rbat05/SolarWeatherStation/code/WeatherStationCode/src/bme280_temp_humi_pres.cpp

#include "bme280_temp_humi_pres.hpp"
#define SENSOR_ADDR 0x76

// Checks if the BME280 sensor is connected
// If connected, the program will continue
// If not, the program will be stuck in an infinite loop until the sensor is
// connected or ESP is reset
void bme280Setup(Adafruit_BME280& bme280) {
  bool status = bme280.begin(SENSOR_ADDR);

  if (status == true) {
    // Serial.printf("BME280 sensor is connected @0x%X!\n", SENSOR_ADDR);
    return;
  } else {
    // Serial.println("BME280 sensor is not connected, check wiring or reset.");
  }
}

// Returns the temperature in Celsius after sampling 100 times
float bme280GetTemperature(Adafruit_BME280& bme280) {
  float rollingSum = 0.0;
  float average = 0.0;
  for (int i = 0; i < 100; i++) {
    rollingSum += bme280.readTemperature();
    delay(10);
  }
  average = rollingSum / 100.0;
  return average;
}

// Returns the humidity in Percentage after sampling 100 times
float bme280GetHumidity(Adafruit_BME280& bme280) {
  float rollingSum = 0.0;
  float average = 0.0;
  for (int i = 0; i < 100; i++) {
    rollingSum += bme280.readHumidity();
    delay(10);
  }
  average = rollingSum / 100.0;
  return average;
}

// Returns the pressure in hPa after sampling 100 times
float bme280GetPressure(Adafruit_BME280& bme280) {
  float rollingSum = 0.0;
  float average = 0.0;
  for (int i = 0; i < 100; i++) {
    rollingSum += bme280.readPressure();
    delay(10);
  }
  average = rollingSum / 10000.0;
  return average;
}

// Changes the sensor mode to sleep mode
void bme280SleepMode() {
  Wire.beginTransmission(SENSOR_ADDR);
  Wire.write((uint8_t)0xF4);  // Selecting the control measurement register
  Wire.write((uint8_t)0b00000000);  // Setting the sensor mode to sleep mode
  Wire.endTransmission();
}

// Changes the sensor mode to forced mode
void bme280ForcedMode() {
  Wire.beginTransmission(SENSOR_ADDR);
  Wire.write((uint8_t)0xF4);  // Selecting the control measurement register
  Wire.write((uint8_t)0b00100101);  // Setting the sensor mode to forced mode
  Wire.endTransmission();
}
