rbat05/SolarWeatherStation/code/WeatherStationCode/src/s12sd_uv.hpp

#ifndef S12SD_UV_HPP
#define S12SD_UV_HPP
#include <Arduino.h>
#include <string.h>

// Gets the UV index value (0-12) based on the sensor value.
int getUVIndexValue(int uv_pin);
// Gets the UV index (LOW-EXTREME) based on the sensor value.
String getUVIndex(int uv_index_value);

float uv_sensor_testing(int uv_pin);
#endif
